villseriol/ATMEGA8A-Tutorial-Board-A/software-design/src/blink_async.cpp

#define __AVR_ATmega8A__ ;

#include <avr/builtins.h>
#include <avr/interrupt.h>
#include <avr/io.h>

#include "common.h"

int main(void)
{
    common::setup();

    __builtin_avr_cli();

    TCCR1A = _BV(COM1A0) | _BV(COM1B0);
    TCCR1B = _BV(CS12);
    TIMSK = _BV(OCIE1A) | _BV(OCIE1B);

    __builtin_avr_sei();

    while (1)
    {
        continue;
    }
}

ISR(TIMER1_COMPA_vect)
{
    OCR1A += HZ_CYCLES(2, 256);
}

ISR(TIMER1_COMPB_vect)
{
    OCR1B += HZ_CYCLES(2, 256);
}
